OPEnSLab-OSU/TutTut/Progress_Report_1/Progress.pdf

## Tut-Tut, The IoT Rain Fall Detector Design Document

Team 21

CS 461 - Fall 2018

Michael Gillett, Casing and Microcontroller Lead

Jonathan Rohr, Data Collection and Management Lead

Shreyans Khunteta, UI Lead

November 26, 2018

## Abstract

Tut-Tut, the IoT Raindrop Detector, is a project under the domain of the OPEnS (Openly Published Environment Sensing) Lab at Oregon State University. Tut-Tut will be able to detect a drop of any size, get an idea of the raindrop mass from the intensity at which it falls, and detect the frequency of raindrops. After Tut-Tut gathers this data, it will be able to wirelessly transmit the information to a central server and communicate it to other IoT devices around Oregon State University. The detector will wake up with a single raindrop and will stay awake as long as rain is detected within a minute. If it does not detect raindrops within a minute, it will go back to sleep. In addition to the physical device, we will also design an online mobile application to which the physical device will transmit information about the raindrops.

## 1 Introduction

This document will go into depth on the progress made in Fall Term regarding our project. Our device is known as Tut-Tut, the IoT (Internet of Things) Rainfall Detector, and will serve the OPEnS Lab’s ecosystem of environmental sensing devices which they call Loom. Tut-Tut will measure the rainfall by reading the mechanical stress of drops hitting its built-in sensor, and relay it to their server using PushingBox technology. The metrics Tut-Tut wants to know are how hard the drops hit the device, and how often a rain drop strikes it. These values will be continually updated into an easily accessible spreadsheet. In the document, we will linearly outline all of our progress so far, discuss all the problems encountered this term, include any plans we have to fix those problems next term in a retrospective table.

## 2 Current Progress & Problems

This term we began work on Tut-Tut in week four, when we were assigned the project. We met with Professor Chet Udell that week and were given an Adafruit Feather M0 microcontroller to work with. Professor Udell told us to have a blinking microcontroller by the next week. We were unable to run any Arduino sketches on our microcontroller and thought initially that it was a problem with our drivers, as it wasn’t working on any of our computers. We had a wide range of laptops and operating systems between us, so that was baffling. We brought it into the OPEnS Lab and the staff discovered the microcontroller we had been given was faulty. We exchanged it for a new one that worked much better and were able to show the microcontroller blinking to Professor Udell and the OPEnS staff minutes after being given an operational microcontroller.

After this, we were told the names of the sensors and transducers we had to acquire. We were able to order them online and have them delivered to Michael Gillett’s Corvallis home. However, Michael was in a horrific car accident on his way to Portland the weekend before Thanksgiving and was stranded there for 8 days. We were unable to open his mailbox and get our equipment, so that delayed us by a week and a half.

We’ve also had some difficulty in being able to meet with Professor Udell due to his busy schedule. We have a set meeting time on Thursdays, but because we started this project midway through the term and because some meetings have to be cancelled abruptly due to Professor Udell’s busy schedule, we haven’t had as much time with him as we would like.

However, we were able to produce a Problem Statement, Requirements document, three detailed Tech Reviews, a Design Document and weekly progress reports since week four. This will help us in setting goals and guidelines for the assignment going forward.

The Problem Statement was used to develop a working definition of the problem we’re solving. Normal rainfall collectors do not provide enough information for the needs of the OPEnS Lab. Our client wants a small, portable, disc-shaped device that can detect and provide detailed information about falling rain in real-time. Information includes rainfall rate, intensity, and density. We also defined Tut-Tut’s eventual goals and use cases for them.

The Requirements document was used to define Tut-Tut’s scope and our eventual goals for it. This was the ”What” document that we used to explain our target audience, our project scope, our business case, user characteristics, assumptions/dependencies and our constraints. The system will be a 2x2 inch waterproof sensor capable of detecting even the most minute amounts of rain. It will have wi-fi or network capabilities and we will be able to integrate it easily with the IoT mesh network around the university. It will be able to detect the size of a raindrop, the frequency at which rain is falling, and the intensity at which it hits the detector.

During the Tech Review, each of us submitted an individual tech review for technologies we are taking responsibility for: data collection and management, microcontroller and 3D printed shell, and coding tools. During these documents we identified the tools we would need to accomplish the task ahead of us, and we explored different alternative methods to implement these different technologies. For example, when listing different usable technologies for the Shell, Michael listed three different potential technologies - Inventor, Onshape and AutoCAD. After exploring each in detail, he explained why we would be using AutoCAD ultimately.

Finally, we wrote the Design Document. In the Design document we described our timeline and explained the design of our project in all respects - the Code Design, the Casing Design, our Data Design (how we would collect

1

and manage data), and our Human Interface Design. We drew upon our previous Tech Review and Requirements documents to properly write this Design Document.

## 3 Pieces of code

/∗
Knock Sensor

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

Th is example code i s in t h e p u b l i c domain .

h t t p : / /www . ar du in o . cc /en / T u t o r i al /Knock
∗/

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

Because of the fact that we have not been able to test our sensors, we have not written any code for the microcontroller yet. We plan to use this example as a basis for Tut-Tut. The ”knock” will be drops of water on the piezoelectric sensor, and the Serial.println function will be the PushingBox API uploading the data to our central server. We also have received a code example using interrupts which could prove useful in letting Tut-Tut sleep when no rain is falling. By having a drop generate an interrupt to wake up the device instead of constantly being active, we could save battery.

2

## Basic Sketch

Figure 1: A basic drawing of what Tut-Tut will resemble when complete

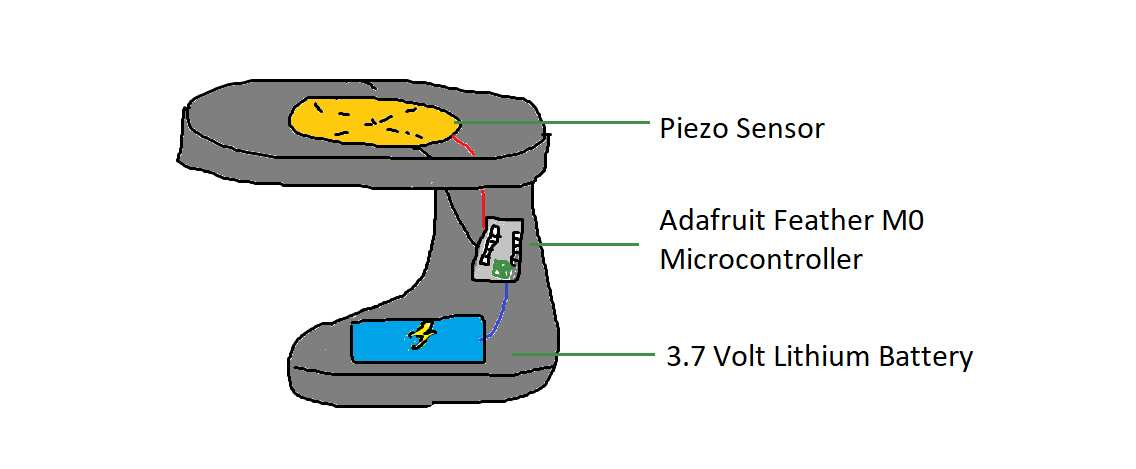
[picture p5: figure]

## 4 Retrospective

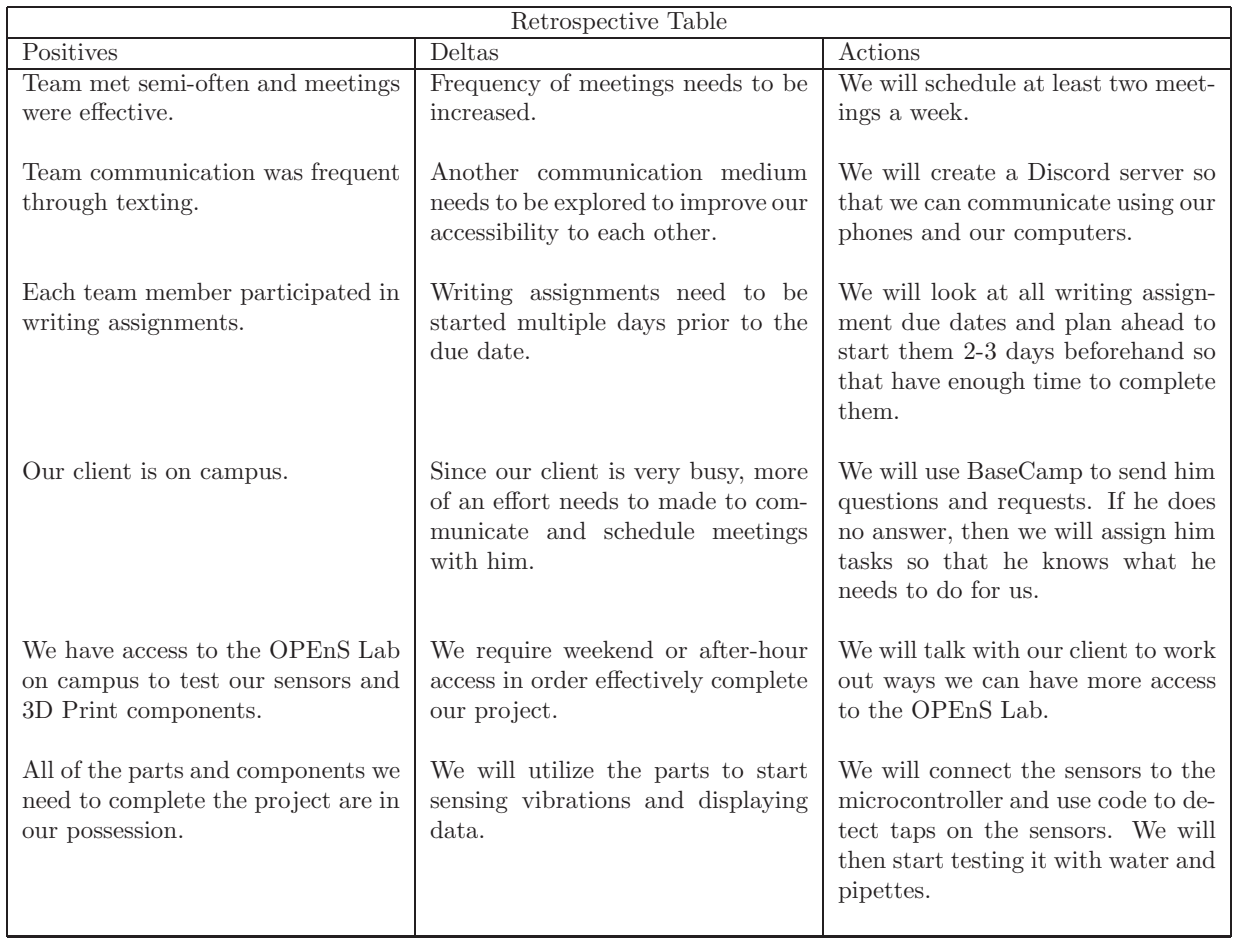
[picture p6: figure]
Retrospective Table; Positives; Deltas; Actions; Team met semi-often and meetings were effective.; Frequency of meetings needs to be increased.; We will schedule at least two meet- ings a week.; Team communication was frequent through texting.; Another communication medium needs to be explored to improve our accessibility to each other.; We will create a Discord server so that we can communicate using our phones and our computers.; Each team member participated in writing assignments.; Writing assignments need to be started multiple days prior to the due date.; We will look at all writing assign- ment due dates and plan ahead to start them 2-3 days beforehand so that have enough time to complete them.; of an effort needs to made to com- municate and schedule meetings with him.; We will use BaseCamp to send him questions and requests. If he does no answer, then we will assign him tasks so that he knows what he needs to do for us.; We have access to the OPEnS Lab on campus to test our sensors and 3D Print components.; We require weekend or after-hour access in order effectively complete our project.; We will talk with our client to work out ways we can have more access to the OPEnS Lab.; All of the parts and components we need to complete the project are in our possession.; We will utilize the parts to start sensing vibrations and displaying data.; We will connect the sensors to the microcontroller and use code to de- tect taps on the sensors. We will then start testing it with water and pipettes.

Our client is on campus. | Since our client is very busy, more

3
