OPEnSLab-OSU/TutTut/Design_Document/Signed_Revised_Design_Document/TutTut_Design_Doc_Revised_Draft_Signed.pdf

## Tut-Tut, The IoT Rain Fall Detector Design Document

Team 21

CS 461 - Fall 2018

Michael Gillett, Casing and Microcontroller Lead

Jonathan Rohr, Data Collection and Management Lead

Shreyans Khunteta, UI Lead

November 26, 2018

## Abstract

Tut-Tut, the IoT Raindrop Detector, is a project under the domain of the OPEnS (Openly Published Environment Sensing) Lab at Oregon State University. Tut-Tut will be able to detect a raindrop of any size, get an idea of the drop’s mass from the intensity at which it falls, and detect the frequency of raindrops. After Tut-Tut gathers this data, it will be able to wirelessly transmit the information to a central server and communicate it to other IoT devices around Oregon State University. The detector will periodically wake up to check for rain and will stay awake as long as rain is detected within two minutes. If it does not detect raindrops within two minutes, it will go back to sleep. As a stretch goal, we will design an online mobile application to which the physical device will transmit information about the raindrops. If this stretch goal is not met, then the data will be stored in a Google Sheet.

## Glossary

OPEnS Lab: Openly Published Environmental Sensing Lab. Located at Oregon State University, this lab’s goal is to develop environmental sensing devices and do research on their findings.

CAD: Computer-Aided Design. CAD is not a single program, but a technique used by many programs to design and simulate 3D objects that will be used in production.

IDE: Integrated Development Environment. Usually refers to the program being used to write and test the coded sections of the project.

IoT: Internet of Things. Used to describe a system made up of interconnected devices that form a network.

Piezo Sensor: Piezoelectric sensor. A device that uses the piezoelectric effect to measure changes in force by converting them to an electrical charge.

MEMS Piezo Vibration Sensor: Microelectromechanical systems sensor. Uses the piezoelectric effect to measure vibrations, but the sensor is small and its components are near microscopic.

Accelerometer: A device that measures vibrations from acceleration forces using electromechanical technology. It measures forces as voltages and then translates those voltages into vibration measurements.

M0 Feather Microcontroller: The M0 Feather is a microcontroller from Adafruit. It is thin, light and the centerpiece of our project. It will be handling all the computing for Tut-Tut.

## Contents

1 Introduction | 3
2 System Overview | 3
3 System Architecture | 3
4 Data Design | 4
5 Human Interface Design | 5
6 Conclusion | 6

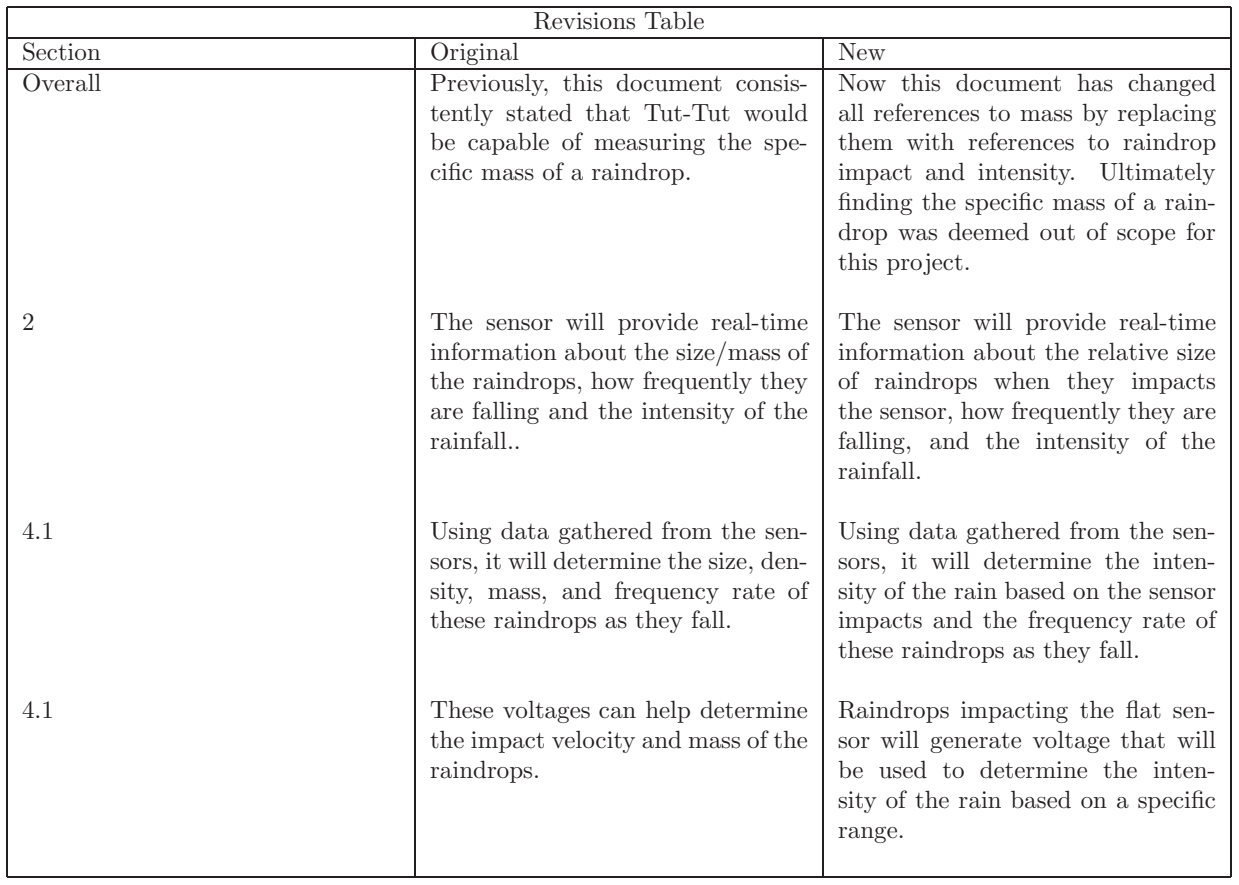
[picture p7: figure]
Revisions Table; Section; Original; New; tently stated that Tut-Tut would be capable of measuring the spe- cific mass of a raindrop.; Now this document has changed all references to mass by replacing them with references to raindrop impact and intensity. Ultimately finding the specific mass of a rain- drop was deemed out of scope for this project.; The sensor will provide real-time; information about the size/mass of the raindrops, how frequently they are falling and the intensity of the rainfall..; The sensor will provide real-time information about the relative size of raindrops when they impacts the sensor, how frequently they are falling, and the intensity of the rainfall.; Using data gathered from the sen-; sors, it will determine the size, den- sity, mass, and frequency rate of these raindrops as they fall.; Using data gathered from the sen- sors, it will determine the inten- sity of the rain based on the sensor impacts and the frequency rate of these raindrops as they fall.; These voltages can help determine; the impact velocity and mass of the raindrops.; Raindrops impacting the flat sen- sor will generate voltage that will be used to determine the inten- sity of the rain based on a specific range.

Overall | Previously, this document consis-

## 1 Introduction

### 1.1 Purpose

This document will outline the design specifications referenced in each of the group members’ Tech Reviews. We will discuss the design of the pieces, technologies, methods, and other parts that will be included in the final product. The final product may differ slightly from the specifications in this document, but it should act as a roadmap moving forward.

### 1.2 Scope

When the Tut-Tut reaches the end of its development, it will be expected to perform three major tasks and one task that will be implemented if there is time. First, it will need to be able to translate vibrations from rainfall into a voltage using its onboard vibration sensors. Second, it will transmit the collected data to the OPEnS Lab’s Dropbox where it is subsequently stored into a spreadsheet in real-time. Third, it must be integrated into their existing ecosystem of sensors, Loom. Finally, if time permits, a browser UI will be used to communicate the Tut-Tut data in an easy to understand way.

### 1.3 Document Overview

First, Michael details the code we will use in our Microcontroller and describes the protective casing that will encase all components of our project. Second, Jonathan describes how we will be collecting rainfall data with sensors and how that data will be sent to our online database. Finally, Shreyans outlines what our stretch goal website would look like. The group members will be primarily responsible for all the technologies in their respective sections for the remaining time frame of the entire project.

## 2 System Overview

This product is designed to accommodate any person(s) who may want to know about rainfall metrics in their area. The sensor will provide real-time information about the voltage when the raindrop falls on the sensor, how frequently they are falling, and the intensity of the rainfall. These metrics could be used by meteorologist as a way to show more detailed information about the rain in the local area. They could also be used by farmers to better take care of their crop fields. Furthermore, the Tut-Tut Rainfall Detector will link into the OPEnS lab’s larger ecosystem of environmental devices and sensors, known as Loom. The data Tut-Tut collects will be stored in a Google Sheets database for analysis.

## 3 System Architecture

### 3.1 Code Design

This section outlines the flow of the code flashed onto the microcontroller.

We will be using an Adafruit Feather M0 microcontroller with Wi-Fi capability. The code that we will use can be divided into two phases: Initialization and Loop. The initialization section will set up all the necessary pins as soon as the device is booted, such as the LED and the analog pin used by the sensor. The looping portion of the code will run continuously, record the necessary data metrics, and upload them to the central server.

Once we test the sensor pieces and can record an accurate output of voltage (about a 1% error), we will have an accurate threshold of voltage that will constitute a raindrop. In the main loop, we will first check the state of the sensor. If the voltage read is above our derived value, the program flow will enter an if-statement that will take care of the uploading. For good measure, we will have a delay function at the end of the loop to avoid overloading the buffer and losing our data.[1]

### 3.2 Casing Design

We have not yet done a model of Tut-Tut, but we do have a few expectations of what it should contain. First, we want the final product to be portable and able to be moved from place to place. To accomplish this we will need room in the casing for a battery, our microcontroller, and the sensor. Since the device will be out in rain, the casing containing the electronics will need to be weatherproof. The shape of Tut-Tut will likely be a 2 cm by 2 cm disk-shaped area on the top for raindrops to fall on, with a heavier base containing the hardware. Figure 1 shows what Tut-Tut might look like at the end of production given these specifications.

Figure 1: A basic drawing of what Tut-Tut will resemble when complete

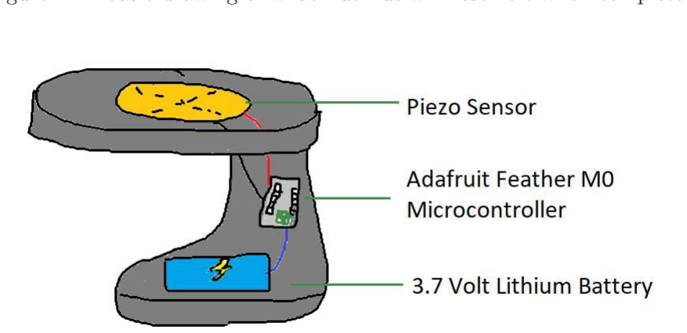
[picture p8: figure]

### 3.3 Design Rationale

Each of the pieces of Tut-Tut had to be chosen specifically regarding the purpose of the final product. Trade-offs were (or will be) made on both the sensor and microcontroller pieces. For the microcontroller, we had the option of a basic board, one with Wi-Fi capability, and one with Long-Range Radio capability. We chose the Wi-Fi model because of the constant connection and reliable transfers of data. The sensors available to us are a piezo, a MEMS, and an accelerometer. These devices are all similar in usage and will only change the specific design of the 3D-printed casing depending on which is chosen.

## 4 Data Design

### 4.1 Data Collection

Tut-Tut will use sensors to register vibrations from raindrops. Using data gathered from the sensors, it will determine the voltage upon impact and frequency rate of these raindrops as they fall. We will be using the Piezo Vibration Sensor and the Piezo Element to accomplish these tasks.

The Piezo Vibration Sensor is a MEMS sensor which uses the piezoelectric effect to detect vibrations. It has dimensions of around 1 cm wide and 2 cm long. It has a high voltage sensitivity of 1 V/g at its baseline and 6 V/g at its resonance. The sensor generates AC and voltage when the thin film gyrates. These voltages can help determine the voltage upon impact of the raindrops, which allows us to see where they fall within a certain range.

The Piezo Element is a basic sensor that also uses the piezoelectric effect to detect vibrations. Raindrops impacting the flat sensor will generate voltage that will be used to determine where the raindrop falls within a certain range. The two sensors perform the same task in different ways, so they each will be tested to determine which one will work best for Tut-Tut.

### 4.2 Data Management

Tut-Tut will be gathering data in the field. This means no one will be around to monitor its results immediately. All of the data that is collected by the sensors above will have to be sent wirelessly, in real-time, to an internet hub. We will use the PushingBox to Google Sheet Pipeline that has already been discovered by the OPEnSLab.[2] As our Arduino Board gathers data from the sensors, it will make GET requests to a PushingBox Scenario using the data to be sent as URL arguments. The PushingBox Scenario formats the data and sends it as URL arguments in its own GET request to the Google Sheet. The Google Sheet will then parse through and display the data. PushingBox currently only supports 1000 requests per day per user. This means that Tut-Tut will only be able to send a string of data once every two minutes.

## 5 Human Interface Design

Currently our scope for the UI is limited. All the information and relevant performance metrics will appear as an Excel spreadsheet you can access through a website link. However, our stretch goal is to create a fully functioning user interface that the user can navigate. This fully functional user interface will be on a website that looks fairly similar to the OPEnS lab website (http://www.open-sensing.org/).

Figure 2: The current OPEnS Lab website. Tut-Tut’s website will resemble this in aesthetic.[3]


### 5.1 Overview of User Interface

This user interface will be built with programming languages such as HTML, CSS and JavaScript. The user interface design is still in progress and it is important to stress that this is a stretch goal. However, we want the final appearance of it to be visually appealing and engaging, and to be be usable and understandable by any educated user, and not just the OPEnS lab staff and students.

### 5.2 Screen Images

The images on the screen will be pictures of OPEnS staff and OPEnS lab projects, such as Tut-Tut itself. It will remain tasteful and aesthetically pleasing, and will incorporate Oregon State logos as well. We will have it try to remain the OPEnS lab webpages themselves.

### 5.3 Screen Objects and Actions

We may implement some minor transitions between pages to make the site look more appealing to the user. However we are not going to use JavaScript effects for the sake of JavaScript effects. We want every transition we do to be for the ultimate comfort and ease of the user. Our design for this will flesh out as the project goes forward, as this is still our stretch goal.

## 6 Conclusion

This document will generally outline the remainder of Tut-Tut’s production and give us a road map in which to reference as needed. First, the code will constantly loop checking for forces read from the Piezo above our calculated threshold, and take appropriate action when an exerted force does cross it. Next, we will have all of our hardware components contained in a waterproof shell that is bottom-heavy with a 2x2 cm disk-shaped surface area to measure the rain drops as they hit. The resulting voltages will be translated into meaningful data and sent through the PushingBox to Google Sheet Pipeline. Finally, if time permits, we will create a UI based off the OPEnS Lab website. It will be easily navigable by any user and will have performance metrics that Tut-Tut will be tracking (raindrop size, intensity and frequency rate). If we are unable to meet this stretch goal, the UI will simply be a Google Sheets document with all the relevant performance metrics.

## References

[1] Arduino, “Arduino Knock Example.” https://www.arduino.cc/en/Tutorial/Knock, accessed 11-26-2018.
[2] O. Lab, “Pushingbox to google sheet pipeline.” https://github.com/OPEnSLab-OSU/InternetOfAg/tree/master/PushingB accessed 11-26-2018.
[3] OPEnS, “OPEnS Lab.” http://www.open-sensing.org/#intro, accessed 11-2-2018.
